poetaster/marvelousMI/firmware/CloudsEngine/Eight.h

// Audio data converted from WAV file by wav2header based on wav2sketch by Paul Stoffregen

// Converted from eight.wav, using 44100 Hz, PCM encoding
#define Eight_SIZE 33068

const int16_t Eight[] = {
   977,  1023,  1076,  1146,  1251,  1340,  1396,  1418,
  1450,  1489,  1522,  1516,  1497,  1460,  1437,  1424,
  1390,  1351,  1323,  1292,  1283,  1249,  1179,  1091,
   999,   931,   898,   871,   833,   796,   737,   661,
   588,   524,   522,   563,   566,   523,   456,   414,
   369,   304,   215,   109,    22,   -25,   -16,    21,
    21,   -30,   -83,  -111,  -109,  -129,  -175,  -209,
  -239,  -247,  -226,  -219,  -227,  -253,  -244,  -201,
  -119,   -67,   -33,   -44,   -73,  -104,   -86,   -57,
   -47,   -77,   -89,   -69,   -43,   -60,   -89,  -109,
  -109,   -89,  -137,  -200,  -273,  -304,  -295,  -259,
  -208,  -223,  -257,  -341,  -415,  -500,  -555,  -585,
  -644,  -748,  -882,  -967,  -967,  -954, -1002, -1110,
 -1196, -1247, -1273, -1336, -1421, -1509, -1534, -1542,
 -1568, -1641, -1728, -1776, -1787, -1799, -1827, -1870,
 -1931, -2001, -2039, -2013, -1940, -1859, -1815, -1776,
 -1736, -1680, -1565, -1416, -1304, -1287, -1275, -1176,
  -978,  -805,  -683,  -558,  -389,  -239,  -124,   -23,
   106,   261,   430,   624,   823,   999,  1147,  1302,
  1494,  1688,  1870,  2049,  2219,  2359,  2455,  2601,
  2779,  2916,  2942,  2967,  3091,  3275,  3423,  3465,
  3427,  3359,  3357,  3423,  3516,  3527,  3498,  3509,
  3564,  3561,  3413,  3275,  3233,  3201,  3069,  2879,
  2695,  2555,  2408,  2248,  2026,  1778,  1511,  1297,
  1082,   838,   570,   343,   161,   -64,  -400,  -748,
  -984, -1183, -1377, -1580, -1803, -2079, -2379, -2625,
 -2804, -2949, -3098, -3305, -3581, -3882, -4126, -4246,
 -4304, -4443, -4690, -4867, -4919, -4877, -4859, -4881,
 -4902, -4886, -4791, -4745, -4749, -4745, -4571, -4282,
 -4057, -4003, -4030, -3932, -3666, -3346, -3124, -2976,
 -2850, -2653, -2391, -2167, -2020, -1856, -1581, -1206,
  -872,  -624,  -370,   -94,   219,   540,   910,  1313,
  1722,  2016,  2176,  2377,  2742,  3152,  3428,  3553,
  3585,  3748,  4096,  4454,  4571,  4525,  4501,  4624,
  4859,  4984,  4880,  4736,  4789,  4998,  5099,  5091,
  5005,  4833,  4687,  4682,  4730,  4799,  4944,  4997,
  4699,  4164,  3779,  3836,  4442,  5280,  6146,  6924,
  6990,  5167,  1602, -1285, -1632,  -729, -1052, -3445,
 -7003, -9702, -9699, -7619, -5853, -5880, -7705, -9819,
-10662,-10842,-11947,-13830,-15663,-17679,-19801,-21231,
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
};
