poetaster/marvelousMI/firmware/CloudsEngine/Five.h

// Audio data converted from WAV file by wav2header based on wav2sketch by Paul Stoffregen

// Converted from five.wav, using 44100 Hz, PCM encoding
#define Five_SIZE 23444

const int16_t Five[] = {
  5322,  5494,  5372,  5066,  4930,  5007,  5059,  4918,
  4621,  4326,  4081,  3780,  3451,  3201,  3048,  2774,
  2294,  1834,  1522,  1126,   564,    76,  -275,  -686,
 -1126, -1408, -1577, -2005, -2665, -3246, -3598, -3817,
 -4055, -4452, -4843, -5108, -5365, -5702, -5892, -5797,
 -5798, -6243, -6698, -6589, -6067, -5589, -5358, -5334,
 -5347, -5350, -5242, -4874, -4348, -4020, -3944, -3720,
 -3039, -2250, -1891, -1793, -1644, -1434, -1154,  -616,
   184,   906,  1271,  1468,  1632,  1759,  1940,  2257,
  2604,  2962,  3384,  3869,  4378,  4781,  4980,  4915,
  4725,  4754,  5165,  5535,  5530,  5279,  5084,  5074,
  5232,  5359,  5189,  4691,  4179,  4020,  4116,  4188,
  4181,  4094,  3789,  3273,  2784,  2626,  2841,  2869,
  2299,  1639,  1546,  1806,  1785,  1422,  1033,   530,
   -64,  -195,   281,   497,   -39,  -777,  -888,  -438,
  -111,  -317,  -774, -1054, -1113, -1147, -1153,  -830,
  -321,  -316,  -889, -1185,  -908,  -688,  -642,   -28,
  1178,  1850,  1498,  1114,  1066,   173, -1685, -2281,
  -449,  1655,  1383, -1129, -3254, -2901,  -282,  2608,
  3870,  3120,  1670,  1307,  2541,  4364,  5512,  5629,
  4901,  3012,   335, -1277,  -988,   808,  3554,  5213,
  3708,   702,   478,  4249,  7170,  5011,  1243,  1008,
  3151,  3958,  2603,   118, -2991, -5682, -5078,  -386,
  3375,  1484, -2694, -2669,  1097,  2583,   596,  -486,
   274,  -549, -3142, -4960, -6263, -8199, -8893, -7458,
 -7427,-10752,-13337,-11736, -8660, -7866, -8689, -9186,
 -8922, -7783, -6921, -9251,-14465,-16877,-12903, -6929,
 -5744, -9791,-13401,-13145,-10510, -6926, -2451,   458,
 -1023, -4335, -4036,  -619,   446,  -958,   -17,  2720,
  2049, -1281, -1364,  1973,  3219,  1860,  2702,  6290,
  8727,  9287,  9327,  7570,  3321,   402,  2153,  6000,
  7483,  5975,  3053,  -319, -2265,  -898,  1898,  2513,
   806,  -919, -2081, -3483, -4494, -3705, -2174, -2473,
 -4262, -4540, -2713, -1882, -3723, -6256, -7573, -7919,
 -7229, -4941, -3198, -5181, -9647,-11515, -8920, -5313,
 -3835, -3856, -3927, -4129, -4277, -3450, -1718,  -396,
  -106,  -191,   130,  1184,  2956,  4885,  6157,  6716,
  6980,  6911,  6937,  8271, 10609, 11416,  9719,  8246,
  9317, 11307, 11428,  9814,  8371,  7649,  7310,  7859,
  9433, 10606, 10177,  8956,  8235,  7802,  6685,  5218,
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
};
