poetaster/marvelousMI/firmware/CloudsEngine/Four.h

// Audio data converted from WAV file by wav2header based on wav2sketch by Paul Stoffregen

// Converted from four.wav, using 44100 Hz, PCM encoding
#define Four_SIZE 33902

const int16_t Four[] = {
 -2975, -2926, -2798, -2722, -2720, -2694, -2621, -2543,
 -2364, -2157, -2099, -2112, -1980, -1772, -1621, -1531,
 -1415, -1246, -1110, -1022,  -896,  -703,  -516,  -322,
  -215,  -135,    24,   278,   466,   626,   796,   916,
  1059,  1317,  1561,  1635,  1673,  1808,  2030,  2248,
  2403,  2492,  2620,  2750,  2813,  2920,  3092,  3227,
  3300,  3322,  3390,  3468,  3500,  3466,  3501,  3557,
  3519,  3414,  3312,  3290,  3321,  3321,  3237,  3071,
  2874,  2710,  2605,  2501,  2334,  2078,  1819,  1679,
  1543,  1264,   945,   713,   487,   161,  -136,  -364,
  -679,  -966, -1138, -1373, -1737, -1975, -2150, -2441,
 -2753, -2924, -3110, -3374, -3607, -3682, -3722, -3838,
 -3956, -4029, -4073, -4115, -4134, -4067, -3991, -3941,
 -3952, -3929, -3770, -3608, -3450, -3179, -2884, -2781,
 -2707, -2397, -2033, -1811, -1597, -1303, -1074,  -793,
  -422,  -154,    -2,   222,   530,   825,  1147,  1450,
  1645,  1818,  2015,  2190,  2309,  2508,  2784,  2918,
  2923,  2966,  3036,  3063,  3121,  3202,  3166,  3026,
  2962,  2934,  2827,  2733,  2755,  2653,  2364,  2122,
  2059,  1930,  1662,  1433,  1263,  1033,   807,   652,
   446,   140,   -23,   -83,  -304,  -573,  -758,  -937,
 -1127, -1229, -1309, -1471, -1580, -1587, -1646, -1767,
 -1806, -1826, -1826, -1793, -1840, -1924, -1824, -1630,
 -1671, -1739, -1519, -1255, -1209, -1137,  -951,  -917,
  -982,  -863,  -613,  -408,  -228,  -111,   -13,   151,
   309,   448,   667,   809,   747,   728,   903,  1081,
  1249,  1453,  1634,  1631,  1400,  1150,  1211,  1419,
  1359,  1294,  1433,  1307,   978,  1036,  1109,   736,
   514,   584,   335,    60,   192,   212,  -143,  -343,
  -458,  -761,  -941,  -978, -1147, -1274, -1251, -1469,
 -1779, -1667, -1416, -1495, -1773, -2003, -2179, -2321,
 -2277, -2004, -1813, -1992, -2258, -2139, -1863, -1855,
 -1916, -1707, -1491, -1534, -1475, -1111,  -697,  -572,
  -765, -1043, -1100,  -938,  -763,  -497,   -76,   141,
  -112,  -383,  -197,   192,   249,   110,    46,    68,
   193,   524,   904,   993,   712,   436,   364,   378,
   587,  1092,  1372,  1194,  1173,  1466,  1550,  1600,
  1802,  1731,  1621,  1882,  1920,  1895,  2565,  2976,
  2401,  2063,  2173,  1789,  1751,  2352,  2084,  1248,
  1561,  2230,  1846,  1514,  1890,  1791,  1104,   791,
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
};
