poetaster/marvelousMI/firmware/CloudsEngine/One.h

// Audio data converted from WAV file by wav2header based on wav2sketch by Paul Stoffregen

// Converted from one.wav, using 44100 Hz, PCM encoding
#define One_SIZE 31607

const int16_t One[] = {
  -540,  -508,   780,  1363,   255, -1221, -2551, -5098,
 -8813,-11350, -9912, -5026, -3506, -8991,-13583,-10052,
 -3343, -2625, -9015,-14462,-12952, -9005,-10054,-16035,
-21696,-24712,-25122,-24633,-24493,-24768,-24927,-24393,
-21755,-17668,-13387, -8907, -5178, -2171,  -678, -2829,
-10453,-19312,-21290,-15549,-11071,-14619,-20923,-19432,
 -8894,  1769,  5119,  1922, -2039, -2614,  -272,  1081,
 -1675, -7188,-12128,-16117,-20251,-21983,-17289, -7891,
   355,  5122,  9189, 14318, 18365, 19863, 20846, 21523,
 18229, 10588,  4737,  4579,  5942,  3769,  -350,  -991,
  3627, 10117, 14967, 17573, 18621, 18833, 18764, 17599,
 13631,  7001,   342, -4140, -6293, -6751, -5692, -3456,
  -963,  2224,  7679, 14290, 18306, 17805, 14458, 10803,
  7326,  3242, -1403, -5928,-10025,-12865,-12423, -7995,
 -1760,  3480,  6531,  7388,  6803,  6032,  5826,  5035,
  1484, -4894,-11168,-14160,-13341,-10443, -7371, -5329,
 -4518, -3780, -1644,  1401,  2485,  -490, -6343,-12204,
-16105,-17458,-16589,-14465,-12091, -9598, -6186, -1294,
  4199,  8316,  9873,  9034,  6448,  3277,   772, -1370,
 -4576, -8851,-11882,-11306, -7098, -1574,  2910,  5876,
  7714,  8539,  8615,  8120,  6119,  1436, -5350,-11788,
-15563,-16011,-13480, -8228, -1293,  5456, 11228, 16778,
 22109, 25261, 25186, 22075, 17192, 11757,  6011,   614,
 -3210, -5023, -4782, -1752,  4387, 11965, 18380, 22516,
 24659, 24878, 22810, 18437, 12386,  5221, -2389, -8510,
-11034, -9755, -5933,  -388,  6440, 13419, 19366, 23524,
 25653, 26137, 24285, 18447, 10772,  2862, -4596,-10210,
-12776,-12672,-10732, -6563,   211,  8097, 14407, 17523,
 17747, 15798, 11908,  6512,    20, -7570,-15413,-21155,
-22634,-20253,-16167,-11622, -6422,  -680,  4595,  8338,
  9818,  8373,  3888, -2495, -9024,-14575,-18801,-21170,
-21034,-18523,-14194, -8431, -1875,  4181,  8541, 10757,
 10759,  8583,  4909,   708, -3674, -8422,-12742,-14655,
-13069, -8991, -4226,   246,  4204,  7343,  9430, 10530,
 10489,  8666,  4979,   699, -2586, -4189, -4124, -2489,
   435,  4258,  8511, 12830, 16693, 19420, 20351, 19270,
 16446, 12434,  8073,  4236,  1367,  -671, -1738, -1183,
  1323,  4890,  8321, 10870, 12311, 12438, 11049,  8210,
  4519,   594, -3106, -5951, -7175, -6453, -4237, -1257,
  2043,  5395,  8399, 10360, 10785,  9608,  6838,  2574,
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
};
