poetaster/marvelousMI/firmware/CloudsEngine/Seven.h

// Audio data converted from WAV file by wav2header based on wav2sketch by Paul Stoffregen

// Converted from seven.wav, using 44100 Hz, PCM encoding
#define Seven_SIZE 21591

const int16_t Seven[] = {
 -2937, -2771, -2774, -2712, -2443, -2102, -1879, -1707,
 -1518, -1362, -1361, -1408, -1308, -1036,  -767,  -588,
  -537,  -581,  -536,  -235,   272,   598,   590,   499,
   590,   892,  1321,  1699,  1803,  1805,  2048,  2424,
  2518,  2392,  2486,  2831,  3075,  3063,  2965,  2864,
  2735,  2611,  2658,  2783,  2692,  2383,  2251,  2435,
  2543,  2364,  2211,  2258,  2262,  2045,  1785,  1629,
  1495,  1466,  1557,  1591,  1394,  1138,   996,   921,
   888,   827,   686,   448,   229,   118,    82,    20,
  -221,  -646, -1062, -1320, -1488, -1696, -1857, -1872,
 -1847, -1990, -2236, -2292, -2097, -1928, -1999, -2164,
 -2244, -2360, -2578, -2619, -2320, -2057, -2204, -2484,
 -2423, -2171, -2071, -2032, -1858, -1682, -1745, -1887,
 -1900, -1692, -1503, -1458, -1414, -1177,  -874,  -680,
  -529,  -290,   -90,   -60,  -122,  -101,   -17,    93,
   241,   442,   604,   717,   872,  1099,  1379,  1616,
  1727,  1740,  1798,  1850,  1838,  1922,  2112,  2214,
  2257,  2312,  2325,  2350,  2554,  2783,  2750,  2540,
  2395,  2334,  2211,  2034,  1971,  2007,  2012,  1858,
  1553,  1269,  1185,  1220,  1124,   875,   621,   399,
   255,   201,   149,    71,    17,  -108,  -331,  -551,
  -723,  -940, -1077, -1113, -1323, -1773, -2082, -2049,
 -2019, -2267, -2610, -2825, -2962, -3092, -3212, -3336,
 -3471, -3578, -3600, -3569, -3550, -3622, -3605, -3522,
 -3578, -3757, -3769, -3647, -3620, -3670, -3657, -3604,
 -3545, -3481, -3424, -3329, -3096, -2819, -2750, -2905,
 -2945, -2602, -1868, -1074,  -673,  -680,  -617,  -421,
  -378,  -327,   -43,   104,   122,   413,   695,   616,
   753,  1434,  2163,  2586,  2606,  2244,  2103,  2885,
  3974,  4159,  3590,  3365,  3762,  4238,  4674,  5014,
  4860,  4328,  3956,  3757,  3732,  4313,  4973,  4911,
  5134,  6813,  9397, 11638, 11672,  9042,  7171,  7610,
  5894,   606, -2309,  -578,   757,  -423,  -442,  1650,
  2562,  2705,  5354,  7119,  1065, -9745,-14130, -8924,
 -2921, -4694,-11966,-15412,-11737, -6789, -4824, -4524,
 -6506,-11991,-17638,-20307,-20034,-17306,-14709,-15165,
-14373, -7323, -1502, -5861,-11548, -5555,  3229, -2858,
-18860,-25101,-19613,-16760,-19453,-16598, -5904,  1334,
  -142, -1397,  3453,  5244, -3781,-15187,-19214,-19918,
-22870,-24856,-22781,-16721, -4831,  9694, 16683, 15000,
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
};
