poetaster/marvelousMI/firmware/CloudsEngine/Six.h

// Audio data converted from WAV file by wav2header based on wav2sketch by Paul Stoffregen

// Converted from six.wav, using 44100 Hz, PCM encoding
#define Six_SIZE 34530

const int16_t Six[] = {
   217,   344,   450,   554,   729,   976,  1229,  1397,
  1500,  1649,  1869,  2091,  2213,  2242,  2318,  2489,
  2673,  2824,  2926,  3023,  3157,  3286,  3383,  3512,
  3610,  3578,  3493,  3447,  3456,  3516,  3533,  3441,
  3313,  3250,  3242,  3264,  3238,  3119,  2952,  2805,
  2730,  2678,  2577,  2464,  2453,  2508,  2475,  2231,
  1844,  1634,  1704,  1627,   977,    -6,  -504,   -94,
   664,   998,   767,   568,   914,  1688,  2487,  2954,
  2125,  -872, -4564, -6628, -6820, -6414, -6700, -8460,
-10823,-12197,-11828, -9947, -8000, -7941, -9695,-11527,
-12853,-14110,-15406,-16415,-17009,-18024,-20028,-21514,
-21136,-19560,-18190,-18010,-18945,-19825,-19959,-19630,
-19113,-19011,-20188,-22681,-25001,-25029,-22614,-19819,
-18953,-20205,-21815,-21524,-18771,-15216,-13071,-13570,
-15802,-17233,-16306,-13661,-11229,-11055,-13392,-16053,
-16635,-14669,-11437, -8841, -8011, -8400, -8329, -6232,
 -2096,  2115,  4377,  4280,  3015,  2231,  2489,  2832,
  2345,  1204,    84,  -164,  1093,  3502,  6126,  8196,
  9477, 10564, 12393, 15032, 17413, 18004, 15936, 12138,
  8790,  7542,  8218,  9232,  9190,  8170,  7600,  9038,
 12883, 17694, 21278, 22384, 21385, 19876, 19265, 19374,
 18647, 15967, 11862,  8224,  6584,  6819,  7604,  8064,
  8420,  9295, 10950, 13196, 15557, 16902, 16231, 13908,
 11236,  9109,  7554,  6239,  4729,  2821,   638, -1044,
 -1307,   221,  2917,  5515,  6789,  6500,  5605,  5293,
  5714,  5872,  4621,  1685, -2314, -6112, -8662, -9777,
-10286,-10900,-11524,-11342, -9820, -7165, -4096, -1368,
   319,   568,  -244, -1424, -2636, -4295, -6840,-10107,
-13441,-16047,-17098,-16163,-13638,-10387, -7175, -4388,
 -2023,   194,  2478,  4512,  5295,  4020,  1088, -2091,
 -4302, -5428, -5837, -5808, -5444, -4718, -3134,  -168,
  3929,  7972, 10651, 11531, 11377, 11091, 11020, 10853,
 10021,  8209,  5821,  4061,  4005,  5611,  7878,  9966,
 11927, 14118, 16765, 19759, 22665, 24730, 25162, 23912,
 21811, 19920, 18516, 17082, 15131, 12832, 10916, 10186,
 10942, 12755, 14802, 16575, 18041, 19400, 20599, 21277,
 21024, 19664, 17408, 14798, 12434, 10530,  8893,  7279,
  5844,  5217,  6054,  8366, 11246, 13399, 14184, 14008,
 13673, 13354, 12570, 10746,  7640,  3519,  -850, -4386,
 -6279, -6737, -6743, -6926, -6967, -6081, -3990, -1276,
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
};
