poetaster/marvelousMI/firmware/CloudsEngine/Two.h

// Audio data converted from WAV file by wav2header based on wav2sketch by Paul Stoffregen

// Converted from two.wav, using 44100 Hz, PCM encoding
#define Two_SIZE 33549

const int16_t Two[] = {
  2035,  2022,  2113,  2310,  2511,  2556,  2358,  2019,
  1773,  1711,  1724,  1613,  1315,   980,   768,   700,
   675,   636,   509,   293,    42,  -126,  -235,  -319,
  -461,  -662,  -924, -1155, -1341, -1529, -1843, -2188,
 -2402, -2450, -2435, -2441, -2514, -2758, -3074, -3230,
 -3117, -2955, -2937, -3028, -3104, -3095, -2985, -2784,
 -2553, -2429, -2510, -2659, -2604, -2276, -1875, -1594,
 -1430, -1362, -1408, -1410, -1169,  -808,  -581,  -552,
  -589,  -562,  -448,  -249,    -3,   200,   305,   348,
   491,   802,  1203,  1527,  1730,  1816,  1810,  1846,
  1908,  1909,  1867,  1930,  2044,  2070,  2023,  2081,
  2146,  2031,  1763,  1598,  1634,  1660,  1497,  1264,
  1150,  1040,   785,   512,   346,   214,    12,  -135,
  -171,  -194,  -272,  -410,  -571,  -723,  -861, -1034,
 -1255, -1519, -1789, -1998, -2143, -2260, -2360, -2418,
 -2465, -2566, -2603, -2506, -2417, -2444, -2490, -2461,
 -2448, -2498, -2490, -2347, -2217, -2207, -2260, -2155,
 -1876, -1599, -1483, -1440, -1313, -1097,  -882,  -714,
  -556,  -359,  -129,    95,   275,   435,   686,  1015,
  1342,  1602,  1828,  2039,  2271,  2571,  2896,  3077,
  3154,  3260,  3448,  3556,  3636,  3773,  3891,  3880,
  3876,  3960,  3989,  3929,  3911,  3967,  4005,  3989,
  3883,  3730,  3616,  3567,  3511,  3460,  3426,  3264,
  3002,  2893,  2926,  2903,  2763,  2536,  2199,  1790,
  1484,  1223,   979,   795,   600,   256,  -106,  -314,
  -515,  -822, -1139, -1411, -1677, -1866, -2013, -2251,
 -2519, -2669, -2798, -2951, -3045, -3162, -3447, -3638,
 -3495, -3279, -3307, -3492, -3635, -3780, -3921, -3951,
 -3866, -3677, -3511, -3434, -3377, -3295, -3227, -3117,
 -2832, -2533, -2432, -2347, -2093, -1831, -1684, -1559,
 -1349, -1089,  -818,  -572,  -310,    16,   167,   258,
   700,  1328,  1463,  1321,  1618,  2148,  2229,  2149,
  2393,  2739,  2916,  2989,  3042,  3160,  3444,  3615,
  3480,  3508,  3845,  4005,  3846,  3738,  3584,  3276,
  3100,  3047,  2866,  2866,  3148,  3029,  2586,  2587,
  2740,  2280,  1890,  2305,  2535,  1865,  1295,  1436,
  1468,   996,   572,   490,   532,   563,   381,    37,
  -128,  -186,  -591,  -994,  -899,  -890, -1297, -1276,
  -736, -1075, -2385, -3263, -3404, -3453, -3201, -2832,
 -3404, -4122, -3401, -1992, -1057,  -217,  -825, -4401,
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
};
