poetaster/marvelousMI/firmware/MarvelousEuro/rings.h

#include "rings/dsp/part.h"
#include "rings/dsp/strummer.h"
#include "rings/dsp/string_synth_part.h"
#include "rings/dsp/dsp.h"

const size_t aBlockSize = rings::kMaxBlockSize;

float rings::Dsp::sr = 48000.0f;
float rings::Dsp::a3 = 440.0f / 48000.0f;


struct Ring {
  rings::Part             part;
  rings::StringSynthPart  string_synth;
  rings::Strummer         strummer;
  rings::PerformanceState performance_state;
  rings::Patch            patch;

  uint16_t                reverb_buffer[32768];

  float                   *silence;
  float                   *out, *aux;     // output buffers
  float                   *input; // input buffer

  bool                    prev_trig;
  int                     prev_poly;

};

struct Ring instance[1];

bool easterEgg = false; // because a button rise takes place, default to true which will be set false just after boot

void updateRingsAudio() {

  rings::Patch *patch = &instance[0].patch;
  rings::PerformanceState *ps = &instance[0].performance_state;

  size_t  size = rings::kMaxBlockSize;

  float gain;
  if (engine_in == 3) {
    gain = global_volume - 0.4f;
  } else if (engine_in == 0) {
    gain = global_volume ;
  } else {
    gain = global_volume ;
  }

  if (easterEgg) {
    gain = global_volume ;
    instance[0].strummer.Process(NULL, size, ps);
    instance[0].string_synth.Process(*ps, *patch, instance[0].silence, instance[0].out, instance[0].aux, size);
  }
  else {
    instance[0].strummer.Process(instance[0].input, size, ps);
    instance[0].part.Process(*ps, *patch, instance[0].input, instance[0].out, instance[0].aux, size);
  }

  for (size_t i = 0; i < size; ++i) {
    // we're reducing to mono since we actually get polyphony for free
    out_bufferL[i] = stmlib::Clip16(static_cast<int32_t>(
          ( ( instance[0].out[i] + instance[0].aux[i] ) * 32768.0f )  * gain ) );
    //out_bufferR[i] = stmlib::Clip16(static_cast<int32_t>( instance[0].aux[i] * 32768.0f)); 
    //out_bufferL[i] = stmlib::Clip16(static_cast<int32_t>((instance[0].out[i]+.11) * 32768.0f)); // was obuff

  }


}

void updateRingsControl() {

  float timbre = (timbre_in + timb_mod);
  CONSTRAIN(timbre, 0.0f, 1.0f);

  float morph = (morph_in + morph_mod);
  CONSTRAIN(morph, 0.0f, 1.0f);

  float harm = (harm_in + harm_mod);
  CONSTRAIN(harm, 0.0f, 1.0f);
  
  float pos = (position_in + pos_mod);
  CONSTRAIN(pos, 0.0f, 1.0f);

  float   *trig_in; // = IN(1);
  float   voct_in = pitch_in * 1.0f;

  float   struct_in = harm ;
  float   bright_in = timbre;
  float   damp_in = morph;

  float   pos_in = pos ;

  short   model = engine_in;
  short   polyphony = 3;
  bool    intern_exciter = true;
  bool    easter_egg = easterEgg;
  bool    bypass = false;

  rings::Patch *patch = &instance[0].patch;
  rings::PerformanceState *ps = &instance[0].performance_state;

  // float   *in = instance[0].input;
  size_t  size = rings::kMaxBlockSize;

  // check input rates for excitation input
 instance[0].input = instance[0].silence;
    // ... and use internal exciter!
 ps->internal_exciter = intern_exciter;

 // pin floats in the middle, if we have swings, sample
 // currently disabled
 /*
  float exc_in = analogRead(CV6) / 4095.0f - 0.45f;
  if (  exc_in > 0.06f ) {
    // intern_exciter should be off, but user can override
    for (size_t i = 0; i < 32; ++i) {
      CV1_buffer[i] = (float) ( ( analogRead(CV6) / 4095.0f ) ) ;
    }
    instance[0].input = CV1_buffer;
    ps->internal_exciter = false;//intern_exciter;
  } else {
    // if there's no audio input, set input to zero...
    instance[0].input = instance[0].silence;
    // ... and use internal exciter!
    ps->internal_exciter = true;
  }*/


  /* from the original with gain foo
    for (size_t i = 0; i < size; ++i) {
    float in_sample = static_cast<float>(input[i].r) / 32768.0f;
    float error, gain;
    error = in_sample * in_sample - in_level;
    in_level += error * (error > 0.0f ? 0.1f : 0.0001f);
    gain = in_level <= kNoiseGateThreshold
         ? (1.0f / kNoiseGateThreshold) * in_level : 1.0f;
    in[i] = gain * in_sample;
    }*/


  if (engine_in == 3 && !easterEgg) polyphony = 1; // the 2op fm freaks out with higher polyphony

  // set resonator model
  CONSTRAIN(model, 0, 5);
  instance[0].part.set_model(static_cast<rings::ResonatorModel>(model));
  instance[0].string_synth.set_fx(static_cast<rings::FxType>(model));

  // set polyphony
  if (polyphony != instance[0].prev_poly) {
    CONSTRAIN(polyphony, 1, 4);
    instance[0].part.set_polyphony(polyphony);
    instance[0].string_synth.set_polyphony(polyphony);
    instance[0].prev_poly = polyphony;
  }

  // set pitch
  CONSTRAIN(voct_in, 0.f, 114.f);
  ps->tonic = 12.f;
  ps->note = voct_in;

  // set params
  CONSTRAIN(struct_in, 0.0f, 1.0f);    //0.9995f
  patch->structure = struct_in;

  float chord = struct_in * (rings::kNumChords - 1);
  instance[0].performance_state.chord = roundf(chord);

  CONSTRAIN(bright_in, 0.0f, 1.0f);
  patch->brightness = bright_in;

  CONSTRAIN(damp_in, 0.0f, 1.0f);
  patch->damping = damp_in;

  CONSTRAIN(pos_in, 0.0f, 1.0f);
  patch->position = pos_in;

  // check trigger input
  bool trigger = (trigger_in == 1.0f);
  bool trigger_flag = (trigger && !instance[0].prev_trig );
  instance[0].prev_trig = trigger;

  if ( trigger_flag) {
    ps->strum = true;
  } else {
    ps->strum = false;
  }
  instance[0].prev_trig = trigger;

 //
  instance[0].part.set_bypass(bypass);

}



// initialize voice parameters
void initRings() {

  //rings::Dsp::setSr(SAMPLERATE); // we removed this

  // allocate memory + init with zeros
  //instance[0].reverb_buffer = (uint16_t*)malloc(32768 * sizeof(uint16_t));
  //memset(instance[0].reverb_buffer, 0, 32768 * sizeof(uint16_t));

  instance[0].silence = (float*)malloc(rings::kMaxBlockSize * sizeof(float));
  memset(instance[0].silence, 0, rings::kMaxBlockSize * sizeof(float));

  instance[0].input = (float*)malloc(rings::kMaxBlockSize * sizeof(float));
  memset(instance[0].input, 0, rings::kMaxBlockSize * sizeof(float));

  instance[0].out = (float *)malloc(rings::kMaxBlockSize * sizeof(float));
  instance[0].aux = (float *)malloc(rings::kMaxBlockSize * sizeof(float));

  // zero out...
  memset(&instance[0].strummer, 0, sizeof(instance[0].strummer));
  memset(&instance[0].part, 0, sizeof(instance[0].part));
  memset(&instance[0].string_synth, 0, sizeof(instance[0].string_synth));

  instance[0].strummer.Init(0.01, 48000.0f / rings::kMaxBlockSize);
  instance[0].part.Init(instance[0].reverb_buffer);
  instance[0].string_synth.Init(instance[0].reverb_buffer);

  instance[0].part.set_polyphony(4);
  instance[0].part.set_model(rings::RESONATOR_MODEL_MODAL);

  instance[0].string_synth.set_polyphony(4);
  instance[0].string_synth.set_fx(rings::FX_FORMANT);
  instance[0].prev_poly = 3;

  instance[0].performance_state.fm = 0.f;       // TODO: fm not used, maybe later...
  instance[0].prev_trig = false;

  // we're fixing this for the moment until we can test with input
  instance[0].performance_state.internal_exciter = true;

  // let's see
  instance[0].performance_state.internal_strum = true;

  updateRingsAudio() ;

  // check input rates
  /*
    if(INRATE(0) == calc_FullRate)
      instance[0].performance_state.internal_exciter = false;
    else
      instance[0].performance_state.internal_exciter = true;

    if(INRATE(1) == calc_ScalarRate)
      instance[0].performance_state.internal_strum = true;
    else
      instance[0].performance_state.internal_sturum = false;

    if(INRATE(2) == calc_ScalarRate)
      instance[0].performance_state.internal_note = true;
    else
      instance[0].performance_state.internal_note = false;
  */

}
