poetaster/marvelousMI/firmware/MarvelousEuro/plaits.h

// plaits dsp

#include "plaits/dsp/dsp.h"
#include "plaits/dsp/voice.h"
//#include "plaits/dsp/oscillator/variable_shape_oscillator.h"
//#include "plaits/dsp/oscillator/variable_shape_oscillator_one.h"


plaits::Modulations modulations;
plaits::Patch patch;
plaits::Voice voice;

//float a0 = (440.0 / 8.0) / kSampleRate; //48000.00;
const size_t   kBlockSize = plaits::kBlockSize;

plaits::Voice::Frame outputPlaits[plaits::kBlockSize];

#define WORKSPACE_SIZE 32756
// ==================== MEMORY BUFFERS ====================
static uint8_t shared_plaits_workspace[WORKSPACE_SIZE] __attribute__((aligned(4)));

struct Unit {
  plaits::Voice       *voice_;
  plaits::Modulations modulations;
  plaits::Patch       patch;
  float               transposition_;
  float               octave_;
  short               trigger_connected;
  short               trigger_toggle;
  bool                last_trig; // from braids

  char                *shared_buffer;
  void                *info_out;
  bool                prev_trig;
  float               sr;
  int                 sigvs;
};

struct Unit voices[1];

// initialize voice parameters
void initPlaits() {
  // init some params
  voices[0].modulations.engine = 0;
  voices[0].patch = patch;
  voices[0].patch.engine = 0;
  voices[0].transposition_ = 0.;
  voices[0].patch.decay = 0.2f;// decay_in; //0.5f;
  voices[0].patch.lpg_colour = lpg_in;

  voices[0].patch.note = 48.0;
  voices[0].patch.harmonics = 0.5;
  voices[0].patch.morph = 0.3;
  voices[0].patch.timbre = 0.3;
  voices[0].last_trig = false;

  voices[0].shared_buffer = (char*)malloc(32756);
  // init with zeros
  memset(voices[0].shared_buffer, 0, 32756);
  stmlib::BufferAllocator allocator(voices[0].shared_buffer, 32756);
  voices[0].voice_ = new plaits::Voice;
  voices[0].voice_->Init(&allocator);
  
  memset(&voices[0].patch, 0, sizeof(voices[0].patch));
  memset(&voices[0].modulations, 0, sizeof(voices[0].modulations));

  // start with no CV input
  voices[0].prev_trig = false;
  
  //voices[0].modulations.timbre_patched = false;  //(INRATE(3) != calc_ScalarRate);
  //voices[0].modulations.morph_patched = false;   // (INRATE(4) != calc_ScalarRate);
  //voices[0].modulations.trigger_patched = false; //(INRATE(5) != calc_ScalarRate);
  //voices[0].modulations.level_patched = false;   // (INRATE(6) != calc_ScalarRate);
  // TODO: we don't have an fm input yet.
  //voices[0].modulations.frequency_patched = false;
  //changePlaitsEngine(0);

}


void updatePlaitsAudio() {
  voices[0].voice_->Render(voices[0].patch, voices[0].modulations,  outputPlaits,  plaits::kBlockSize);
}

void updatePlaitsControl() {
  
  float modulation;
  
  float timbre = (timbre_in + timb_mod);
  CONSTRAIN(timbre, 0.0f, 1.0f);

  float morph = (morph_in + morph_mod);
  CONSTRAIN(morph, 0.0f, 1.0f);

  float harm = (harm_in + harm_mod);
  CONSTRAIN(harm, 0.0f, 1.0f);

/*  if (pos_mod < 0.02) {
    modulation = 1.0f;
  } else {
    modulation = pos_mod;
  }
  float harm = (harm_in + pos_mod);
  */

  voices[0].patch.engine = engine_in;
  voices[0].patch.note = pitch_in;
  voices[0].patch.harmonics = harm;
  voices[0].patch.morph = morph;
  voices[0].patch.timbre = timbre;
  //voices[0].patch.timbre_modulation_amount = timb_mod;
  //voices[0].patch.morph_modulation_amount = morph_mod;
  //
  voices[0].patch.lpg_colour = 0.2f;//lpg_in;
  voices[0].patch.decay = 0.5f;

  /*
    voices[0].octave_ = octave_in;
    voices[0].patch.lpg_colour = 0.2;
  */
}

void updateVoicetrigger() {
  bool trig = (trigger_in == 1.0f);
  bool trigger_flag = (trig && (!voices[0].last_trig));

  if (trigger_flag) {
    voices[0].modulations.level = 1.0f;
    voices[0].modulations.level_patched = true;
    voices[0].modulations.trigger = 1.0f;
    voices[0].modulations.trigger_patched = true;

  } else {
    voices[0].modulations.trigger_patched = false;
    voices[0].modulations.trigger = 0.0f;
  }
  voices[0].last_trig = trig;
}
