poetaster/marvelousMI/firmware/MarvelousEuro/names.h

const char* const oscnames[] = {
   "Virtual Analog", "Waveshaping", "FM", "Grain", "Additive", "Wavetable", "Chord", "Speech",
  "Swarm", "Noise", "Particle", "String", "Modal", "Bass Drum", "Snare Drum", "Hi-Hat", 
  "Six OP 0", "Six OP 1", "Six OP 2","Virtual Analog VCF", "Phase Distortion", "Wave Terrain"
  };
 /* 
  "V-Analog",
  "Wv-Shape",
  "FM",
  "Grains",
  "Add",
  "Wv-Table",
  "Chord",
  "Speech",
  "Swarm",
  "Noise",
  "Partcl",
  "String",
  "Modal",
  "Wv-Terain",
  "VA-VCF",
  "PhaseDist",
  "BASSD",
  "SNARED",
  "HI-HAT",
}; 

*/

const size_t nameslength = sizeof(oscnames) / sizeof(oscnames[0]);


const char* const modelnames[] = {
  "Modal Reso",
  "Sympa String",
  "Modulated String",
  "2OP FM",
  "Sympa String Q",
  "String & Verb"
};
 
const char* const FXnames[] = {
  "FX Formant",
  "FX Chorus",
  "FX Reverb",
  "FX Formant",
  "FX Ensemble",
  "FX Reverb"
};


const size_t modelslength = sizeof(modelnames) / sizeof(modelnames[0]);

const char* const cloudnames[] = {
  "GRANULAR",
  "STRETCH",
  "LOOPING",
  "SPECTRAL"
};
const size_t cloudnameslength = sizeof(cloudnames) / sizeof(cloudnames[0]);

const char* const braidsnames[] = {
  "CSAW",
  "MORPH",
  "SAW_SQUARE",
  "SINE_TRIANGLE",
  "BUZZ",
  "SQUARE_SUB",
  "SAW_SUB",
  "SQUARE_SYNC",
  "SAW_SYNC",
  "TRIPLE_SAW",
  "TRIPLE_SQUARE",
  "TRIPLE_TRIANGLE",
  "TRIPLE_SINE",
  "TRIPLE_RING_MOD",
  "SAW_SWARM",
  "SAW_COMB",
  "TOY",
  "LP FILTER",
  "PK FILTER",
  "BP FILTER",
  "HP FILTER",
  "VOSIM",
  "VOWEL",
  "VOWEL_FOF",
  "HARMONICS",
  "FM",
  "FEEDBACK_FM",
  "CHAOTIC_FEEDBACK_FM",
  "PLUCKED",
  "BOWED",
  "BLOWN",
  "FLUTED",
  "STRUCK_BELL",
  "STRUCK_DRUM",
  "KICK",
  "CYMBAL",
  "SNARE",
  "WAVETABLES",
  "Wave Map",
  "Wave Line",
  "Wave Paraphonic",
  "FILTERED_NOISE",
  "TWIN_PEAKS_NOISE",
  "CLOCKED_NOISE",
  "GRANULAR_CLOUD",
  "PARTICLE_NOISE",
};

const size_t braidslength = sizeof(braidsnames) / sizeof(braidsnames[0]);
